mathisfun2048/PaperCam/assets/IMG_4885.png

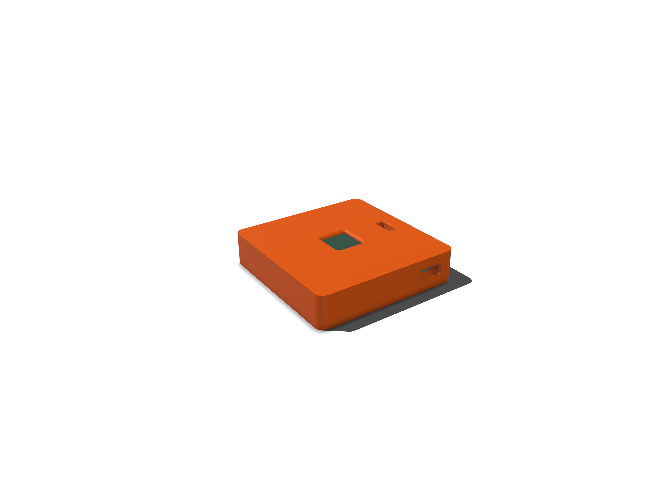
assets/IMG_4885.png
