mathisfun2048/PaperCam/assets/IMG_4886.jpeg

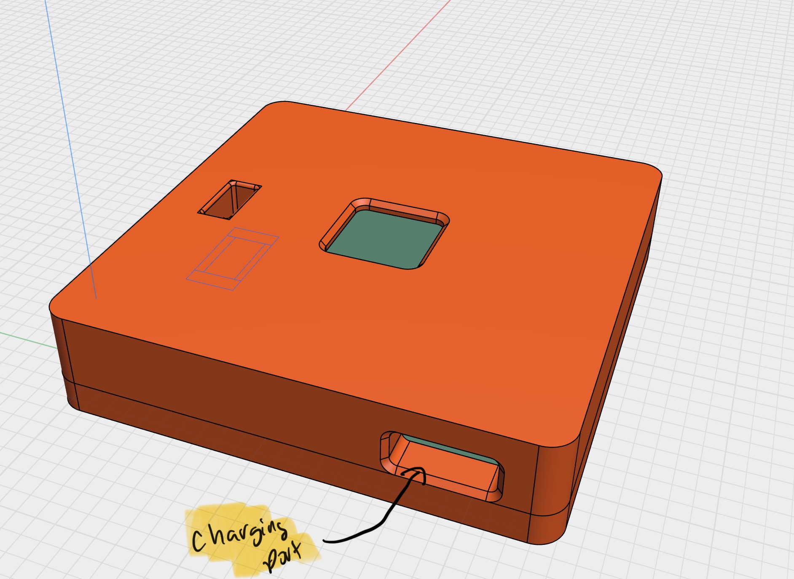
assets/IMG_4886.jpeg
