mathisfun2048/PaperCam/assets/IMG_4891.jpeg

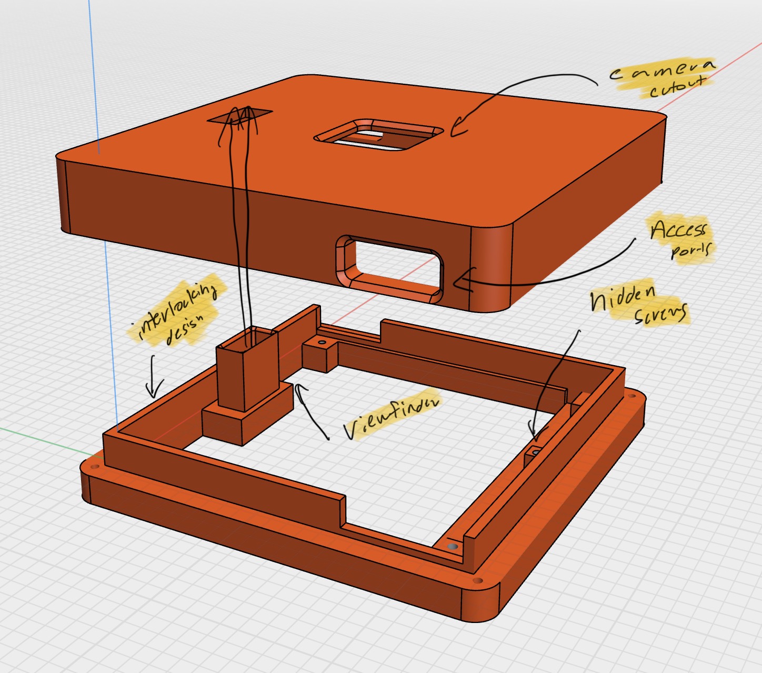
assets/IMG_4891.jpeg
